Oluwaseunemme/ESP32-BLE-Multi-Meter/Arduino_passive_multi_meter/pcb_sch_imag/MeterSchPcb_kicad_routed_latest_back.png

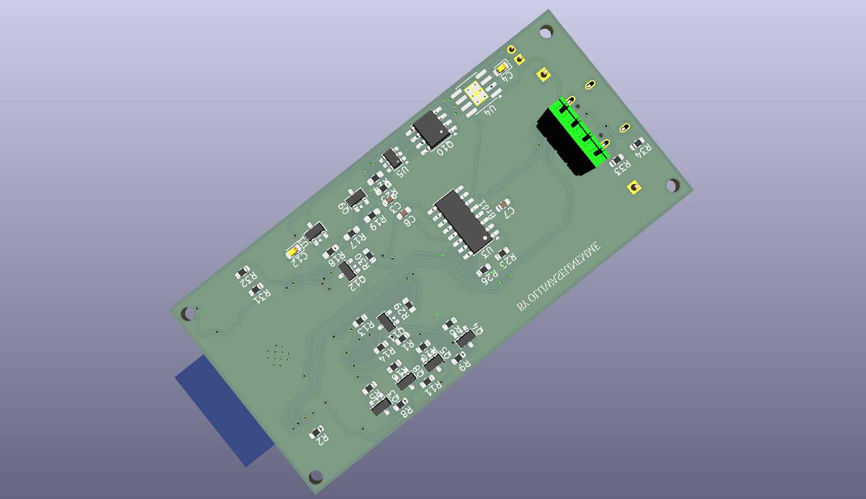
Arduino_passive_multi_meter/pcb_sch_imag/MeterSchPcb_kicad_routed_latest_back.png
