Oluwaseunemme/ESP32-BLE-Multi-Meter/Arduino_passive_multi_meter/pcb_sch_imag/photo_2026-09-27_13-16-23.jpg

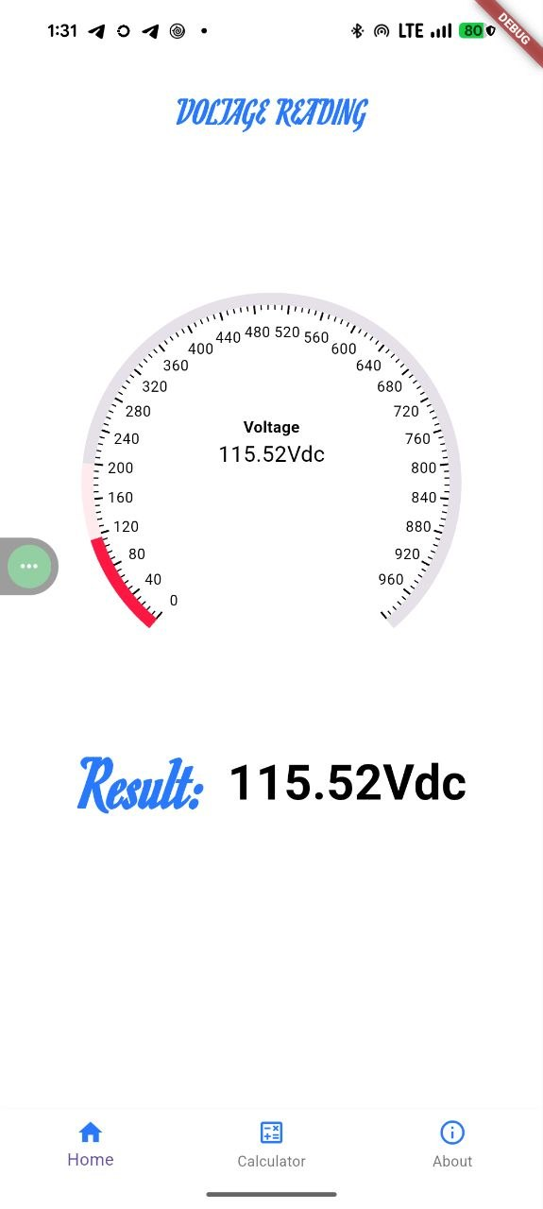
Arduino_passive_multi_meter/pcb_sch_imag/photo_2026-09-27_13-16-23.jpg
