Oluwaseunemme/ESP32-BLE-Multi-Meter/Arduino_passive_multi_meter/pcb_sch_imag/Screenshot 2026-09-20 142119.png

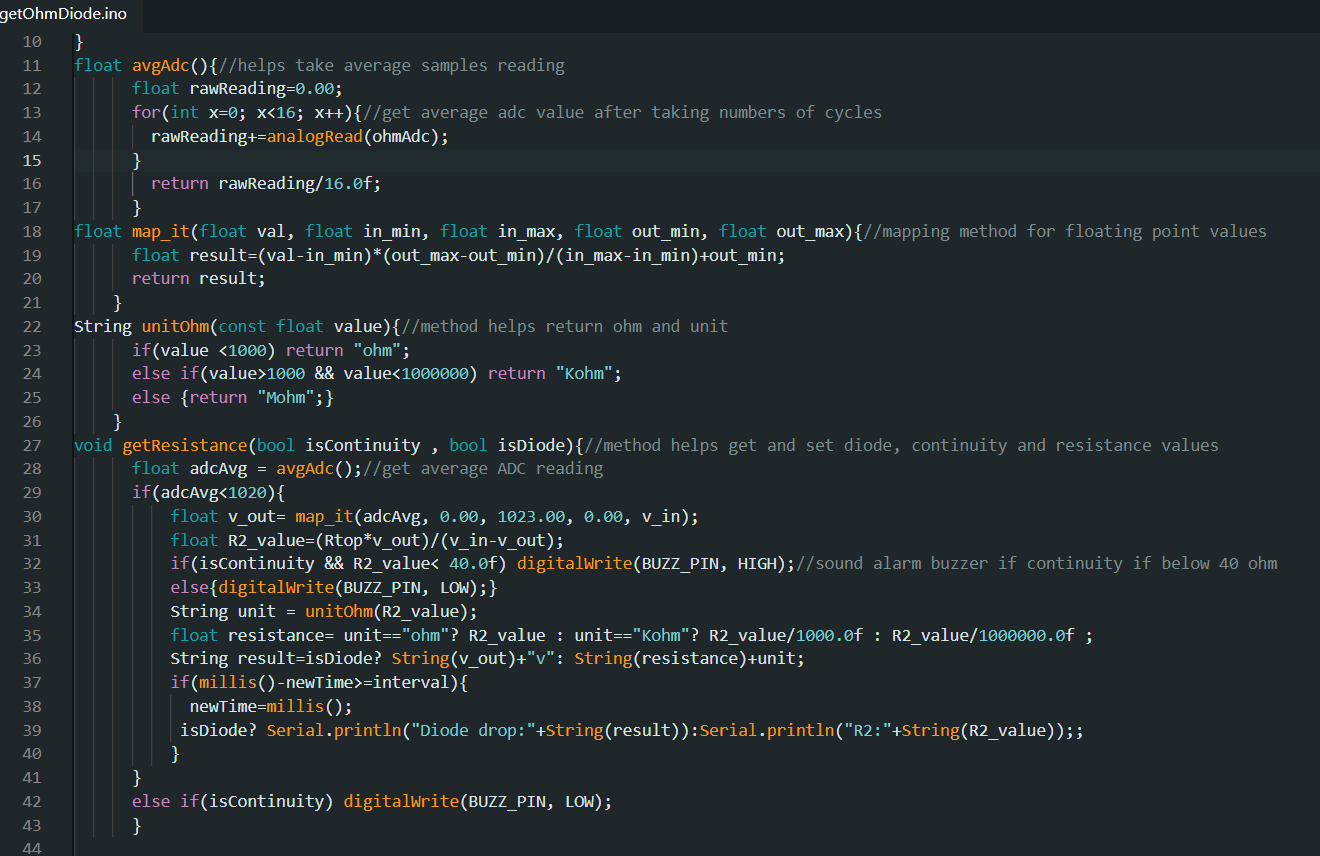
Arduino_passive_multi_meter/pcb_sch_imag/Screenshot 2026-09-20 142119.png
